jonathanedgecombe/imo-proxy/firmware/Descriptors.c

/*
             LUFA Library
     Copyright (C) Dean Camera, 2017.

  dean [at] fourwalledcubicle [dot] com
           www.lufa-lib.org
*/

/*
  Copyright 2017  Dean Camera (dean [at] fourwalledcubicle [dot] com)

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
  The author disclaims all warranties with regard to this
  software, including all implied warranties of merchantability
  and fitness.  In no event shall the author be liable for any
  special, indirect or consequential damages or any damages
  whatsoever resulting from loss of use, data or profits, whether
  in an action of contract, negligence or other tortious action,
  arising out of or in connection with the use or performance of
  this software.
*/

#include "Descriptors.h"

const USB_Descriptor_HIDReport_Datatype_t PROGMEM MouseReport[] = {
	0x05, 0x01,        // Usage Page (Generic Desktop Ctrls)
	0x09, 0x02,        // Usage (Mouse)
	0xA1, 0x01,        // Collection (Application)
	0x09, 0x01,        //   Usage (Pointer)
	0xA1, 0x00,        //   Collection (Physical)
	0x05, 0x09,        //     Usage Page (Button)
	0x19, 0x01,        //     Usage Minimum (0x01)
	0x29, 0x05,        //     Usage Maximum (0x05)
	0x15, 0x00,        //     Logical Minimum (0)
	0x25, 0x01,        //     Logical Maximum (1)
	0x95, 0x05,        //     Report Count (5)
	0x75, 0x01,        //     Report Size (1)
	0x81, 0x02,        //     Input (Data,Var,Abs,No Wrap,Linear,Preferred State,No Null Position)
	0x95, 0x01,        //     Report Count (1)
	0x75, 0x03,        //     Report Size (3)
	0x81, 0x03,        //     Input (Const,Var,Abs,No Wrap,Linear,Preferred State,No Null Position)
	0x05, 0x01,        //     Usage Page (Generic Desktop Ctrls)
	0x09, 0x30,        //     Usage (X)
	0x09, 0x31,        //     Usage (Y)
	0x09, 0x38,        //     Usage (Wheel)
	0x15, 0x81,        //     Logical Minimum (-127)
	0x25, 0x7F,        //     Logical Maximum (127)
	0x75, 0x08,        //     Report Size (8)
	0x95, 0x03,        //     Report Count (3)
	0x81, 0x06,        //     Input (Data,Var,Rel,No Wrap,Linear,Preferred State,No Null Position)
	0xC0,              //   End Collection
	0xC0,              // End Collection
};

const USB_Descriptor_Device_t PROGMEM DeviceDescriptor = {
	.Header               = {.Size = sizeof(USB_Descriptor_Device_t), .Type = DTYPE_Device},

	.USBSpecification     = VERSION_BCD(1,1,0),
	.Class                = USB_CSCP_NoDeviceClass,
	.SubClass             = USB_CSCP_NoDeviceSubclass,
	.Protocol             = USB_CSCP_NoDeviceProtocol,

	.Endpoint0Size        = FIXED_CONTROL_ENDPOINT_SIZE,

	.VendorID             = 0x6666,
	.ProductID            = 0x727F,
	.ReleaseNumber        = VERSION_BCD(0,0,1),

	.ManufacturerStrIndex = STRING_ID_Manufacturer,
	.ProductStrIndex      = STRING_ID_Product,
	.SerialNumStrIndex    = NO_DESCRIPTOR,

	.NumberOfConfigurations = FIXED_NUM_CONFIGURATIONS
};

const USB_Descriptor_Configuration_t PROGMEM ConfigurationDescriptor = {
	.Config = {
			.Header                 = {.Size = sizeof(USB_Descriptor_Configuration_Header_t), .Type = DTYPE_Configuration},

			.TotalConfigurationSize = sizeof(USB_Descriptor_Configuration_t),
			.TotalInterfaces        = 1,

			.ConfigurationNumber    = 1,
			.ConfigurationStrIndex  = NO_DESCRIPTOR,

			.ConfigAttributes       = (USB_CONFIG_ATTR_RESERVED | USB_CONFIG_ATTR_SELFPOWERED),

			.MaxPowerConsumption    = USB_CONFIG_POWER_MA(500)
		},

	.HID_Interface = {
			.Header                 = {.Size = sizeof(USB_Descriptor_Interface_t), .Type = DTYPE_Interface},

			.InterfaceNumber        = INTERFACE_ID_Mouse,
			.AlternateSetting       = 0x00,

			.TotalEndpoints         = 1,

			.Class                  = HID_CSCP_HIDClass,
			.SubClass               = HID_CSCP_BootSubclass,
			.Protocol               = HID_CSCP_MouseBootProtocol,

			.InterfaceStrIndex      = NO_DESCRIPTOR
		},

	.HID_MouseHID = {
			.Header                 = {.Size = sizeof(USB_HID_Descriptor_HID_t), .Type = HID_DTYPE_HID},

			.HIDSpec                = VERSION_BCD(1,1,1),
			.CountryCode            = 0x00,
			.TotalReportDescriptors = 1,
			.HIDReportType          = HID_DTYPE_Report,
			.HIDReportLength        = sizeof(MouseReport)
		},

	.HID_ReportINEndpoint = {
			.Header                 = {.Size = sizeof(USB_Descriptor_Endpoint_t), .Type = DTYPE_Endpoint},

			.EndpointAddress        = MOUSE_EPADDR,
			.Attributes             = (EP_TYPE_INTERRUPT | ENDPOINT_ATTR_NO_SYNC | ENDPOINT_USAGE_DATA),
			.EndpointSize           = MOUSE_EPSIZE,
			.PollingIntervalMS      = 1
		}
};

const USB_Descriptor_String_t PROGMEM LanguageString = USB_STRING_DESCRIPTOR_ARRAY(LANGUAGE_ID_ENG);
const USB_Descriptor_String_t PROGMEM ManufacturerString = USB_STRING_DESCRIPTOR(L"jpe");
const USB_Descriptor_String_t PROGMEM ProductString = USB_STRING_DESCRIPTOR(L"mouseproxy");

uint16_t CALLBACK_USB_GetDescriptor(const uint16_t wValue, const uint16_t wIndex, const void** const DescriptorAddress) {
	const uint8_t  DescriptorType   = (wValue >> 8);
	const uint8_t  DescriptorNumber = (wValue & 0xFF);

	const void* Address = NULL;
	uint16_t    Size    = NO_DESCRIPTOR;

	switch (DescriptorType) {
		case DTYPE_Device:
			Address = &DeviceDescriptor;
			Size    = sizeof(USB_Descriptor_Device_t);
			break;

		case DTYPE_Configuration:
			Address = &ConfigurationDescriptor;
			Size    = sizeof(USB_Descriptor_Configuration_t);
			break;

		case DTYPE_String:
			switch (DescriptorNumber) {
				case STRING_ID_Language:
					Address = &LanguageString;
					Size    = pgm_read_byte(&LanguageString.Header.Size);
					break;

				case STRING_ID_Manufacturer:
					Address = &ManufacturerString;
					Size    = pgm_read_byte(&ManufacturerString.Header.Size);
					break;

				case STRING_ID_Product:
					Address = &ProductString;
					Size    = pgm_read_byte(&ProductString.Header.Size);
					break;
			}
			break;

		case HID_DTYPE_HID:
			Address = &ConfigurationDescriptor.HID_MouseHID;
			Size    = sizeof(USB_HID_Descriptor_HID_t);
			break;

		case HID_DTYPE_Report:
			Address = &MouseReport;
			Size    = sizeof(MouseReport);
			break;
	}

	*DescriptorAddress = Address;
	return Size;
}
